Ratamuse/Testboard/3D/47371.png

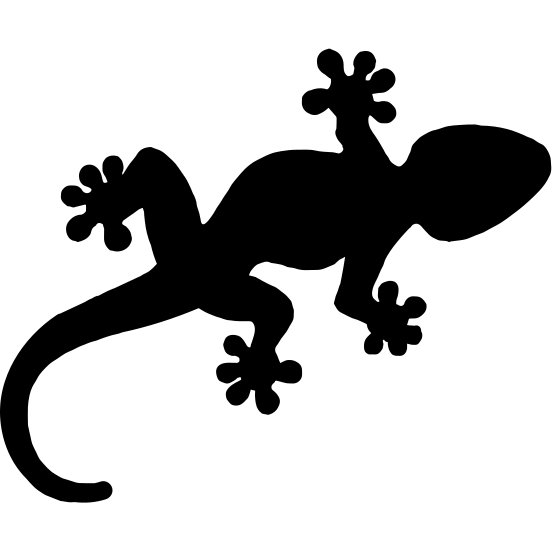
3D/47371.png
