Ratamuse/Testboard/3D/DW01.stp

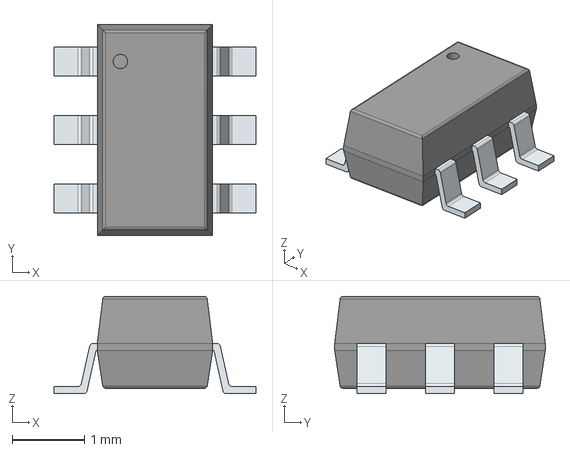
[picture p18: CAD file, 2021-10-16]
3D/DW01.stp
2.80 x 2.92 x 1.35 mm
PinsArrayLR
