Ratamuse/Testboard/3D/B3B-PH-K-S.STEP

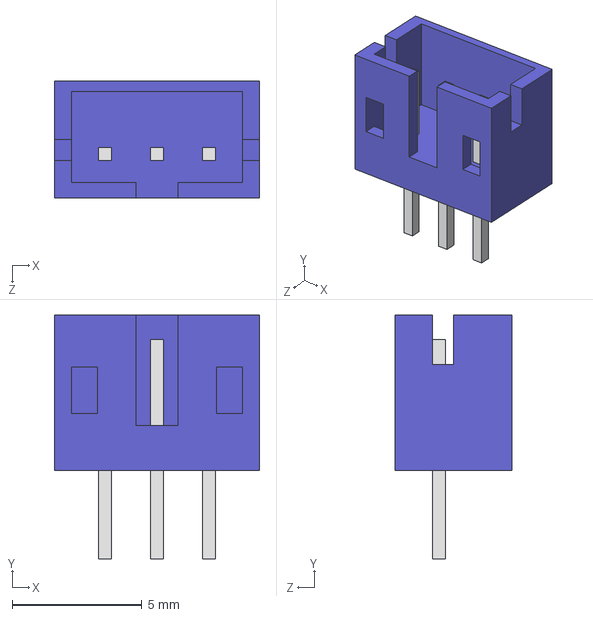
[picture p19: CAD file, 2021-10-16]
3D/B3B-PH-K-S.STEP
7.90 x 9.40 x 4.50 mm
