Ratamuse/Testboard/3D/AO3400.stp

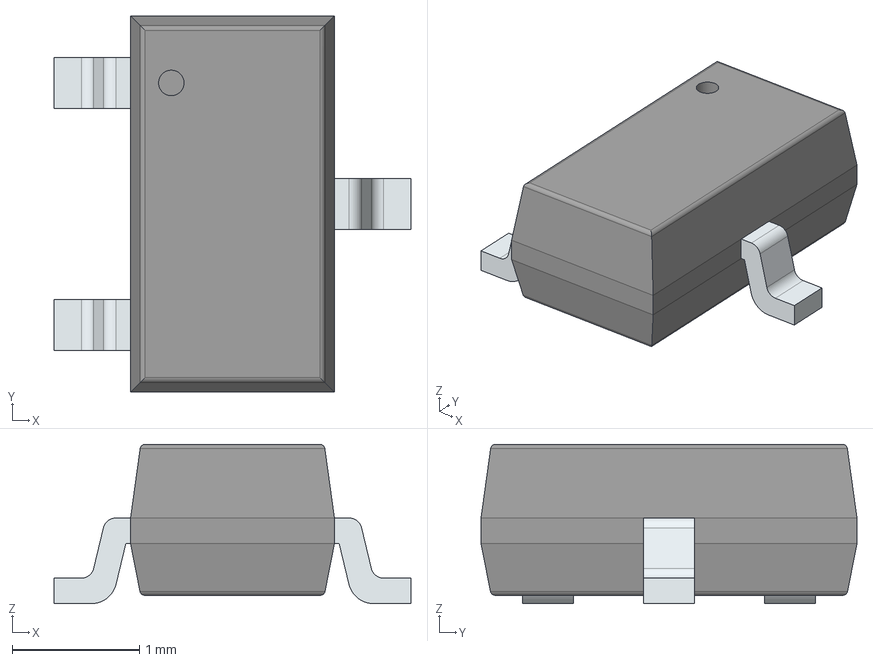
[picture p20: CAD file, 2021-10-16]
3D/AO3400.stp
2.80 x 2.95 x 1.25 mm
PinsArrayL
FilletPinR
