Ratamuse/Testboard/3D/B4B-PH-SM4-TB.STEP

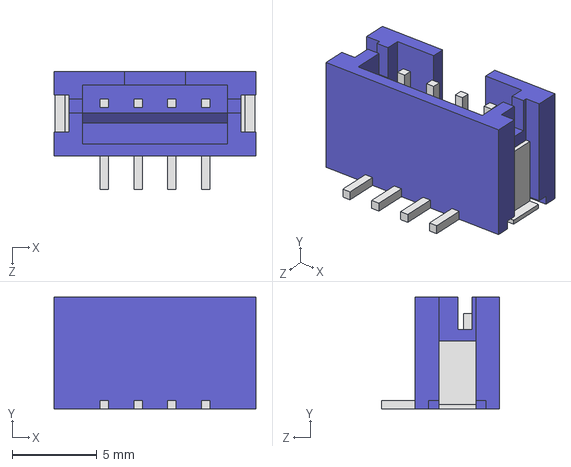
[picture p21: CAD file, 2021-10-16]
3D/B4B-PH-SM4-TB.STEP
12.0 x 6.60 x 7.00 mm
