Ratamuse/Testboard/3D/User Library-PC817_Gullwing.STEP

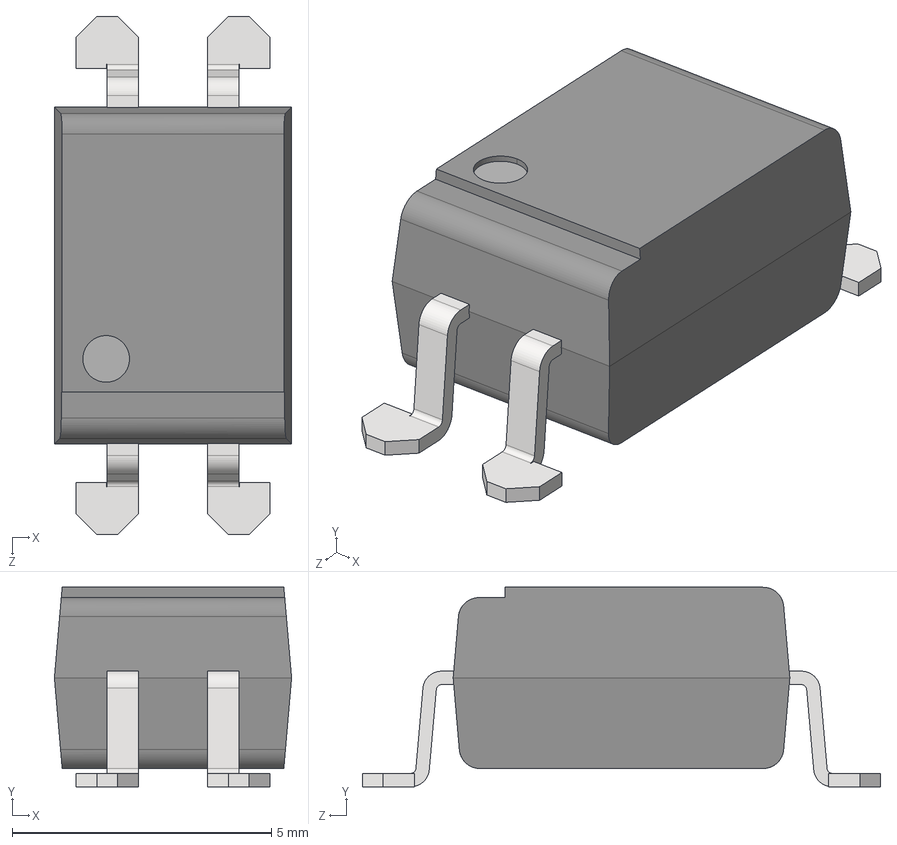
[picture p22: CAD file, 2021-10-16]
3D/User Library-PC817_Gullwing.STEP
4.58 x 3.85 x 10.0 mm
PC817 Body
Gullwing Pin
Gullwing Pin_MIR
Gullwing Pin_MIR1
Gullwing Pin_MIR_MIR
