Ratamuse/Testboard/3D/FS312F-G.stp

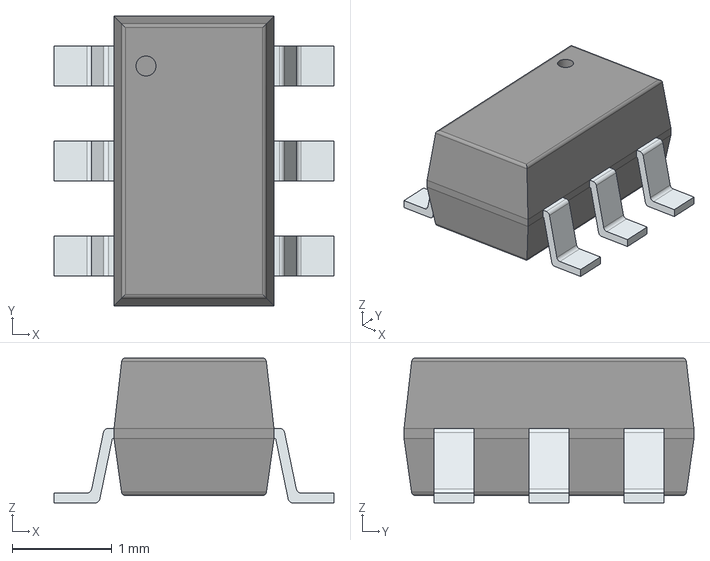
[picture p23: CAD file, 2021-10-16]
3D/FS312F-G.stp
2.80 x 2.90 x 1.45 mm
PinsArrayLR
