Ratamuse/Testboard/3D/ESP32-WROOM-32E_M113EH2800PH3Q0_.stp

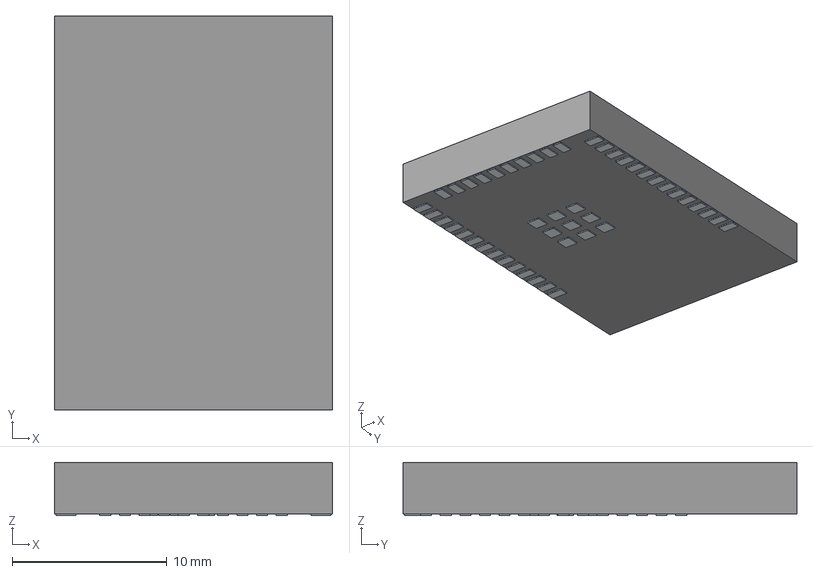
[picture p24: CAD file, 2021-10-16]
3D/ESP32-WROOM-32E_M113EH2800PH3Q0_.stp
18.0 x 25.5 x 3.45 mm
Pins
