Ratamuse/Testboard/3D/USB4105-GF-A--3DModel-STEP-56544.STEP

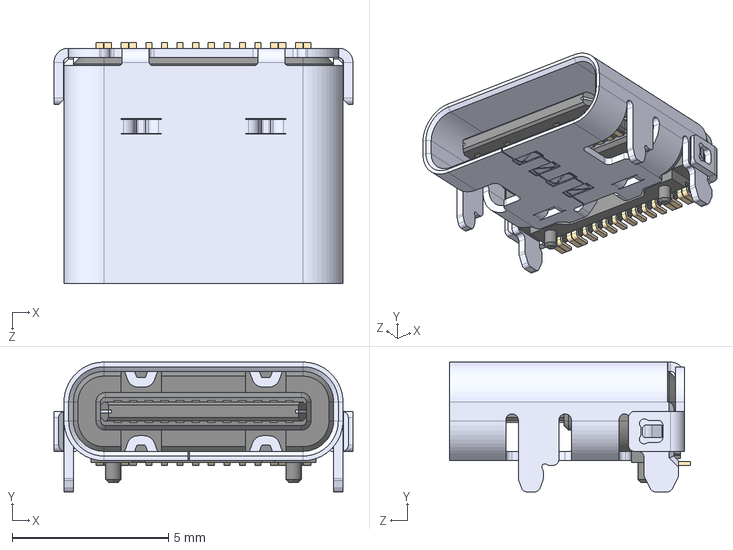
[picture p25: CAD file, 2021-10-16]
3D/USB4105-GF-A--3DModel-STEP-56544.STEP
9.58 x 4.16 x 7.71 mm
