Ratamuse/Testboard/3D/BME680.step

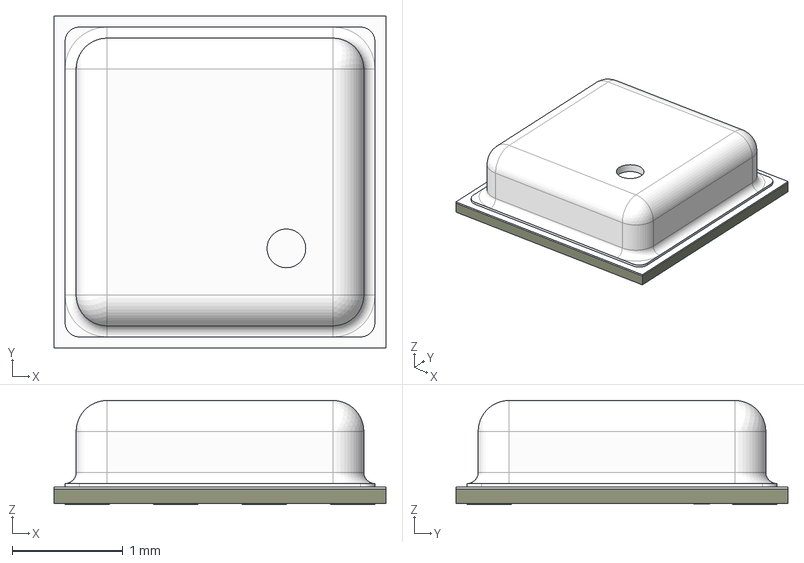
[picture p26: CAD file, 2021-10-16]
3D/BME680.step
3.00 x 3.00 x 0.94 mm
pads
pcb
lid
