Ratamuse/Testboard/3D/LTC2954CTS8-1#TRMPBF.stp

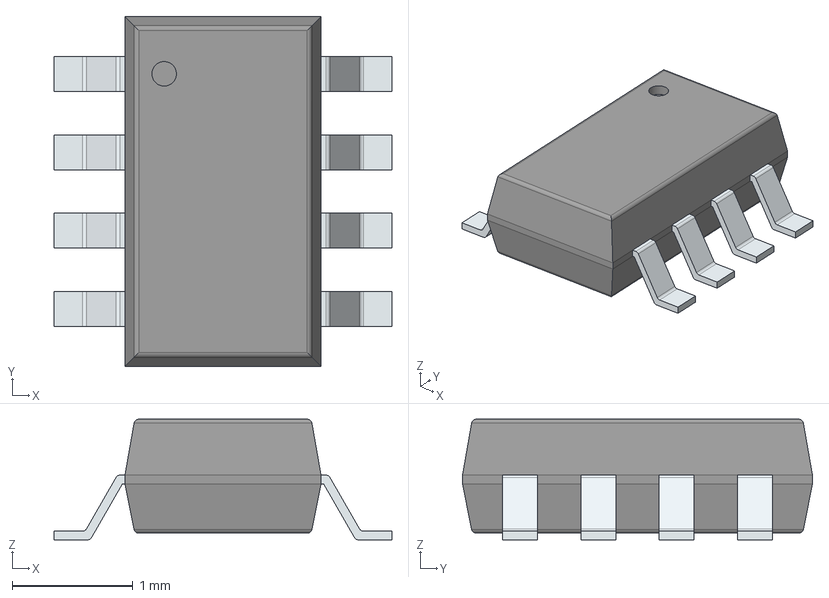
[picture p27: CAD file, 2021-10-16]
3D/LTC2954CTS8-1#TRMPBF.stp
2.80 x 2.90 x 1.00 mm
PinsArrayLR
